berliarishabh/Mobile-Computing-and-IoT-Security----Final-Project-Repo/Photos and Screenshots/EnergyProfile_ScreenShots/BLE_OFF,SENSORS_ON.png

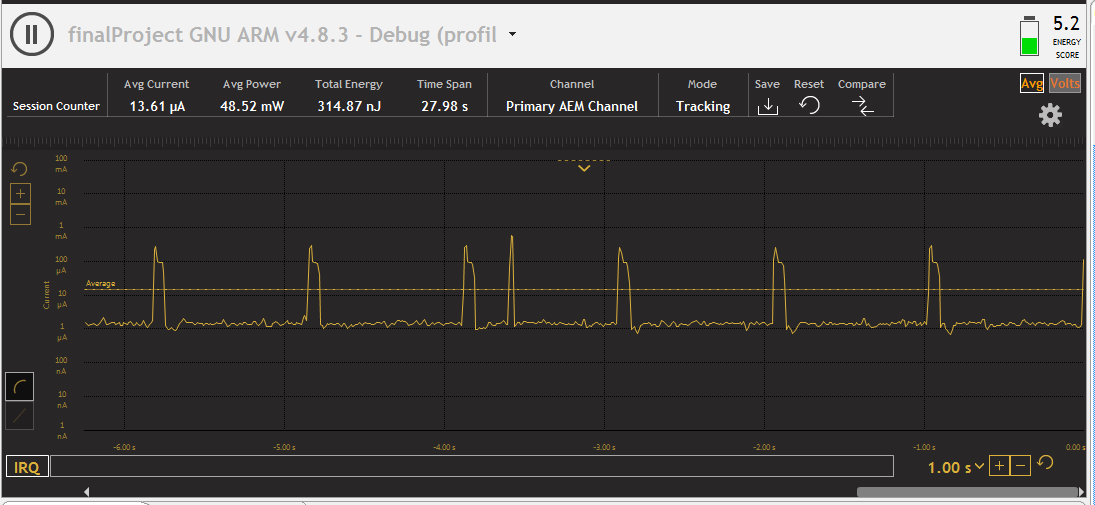
Photos and Screenshots/EnergyProfile_ScreenShots/BLE_OFF,SENSORS_ON.png
