berliarishabh/Mobile-Computing-and-IoT-Security----Final-Project-Repo/Photos and Screenshots/EnergyProfile_ScreenShots/Cap.png

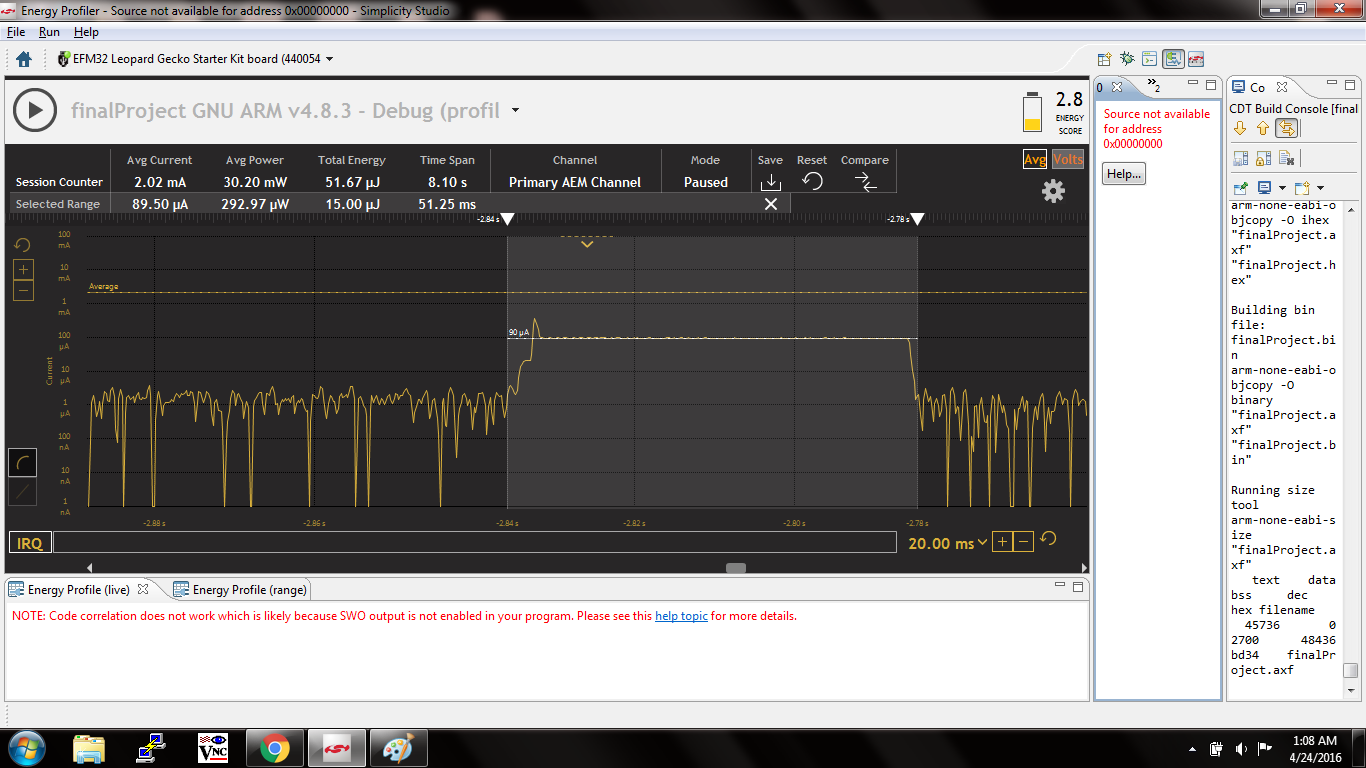
Photos and Screenshots/EnergyProfile_ScreenShots/Cap.png
