berliarishabh/Mobile-Computing-and-IoT-Security----Final-Project-Repo/Photos and Screenshots/EnergyProfile_ScreenShots/LC,Light,Cap-ON.png

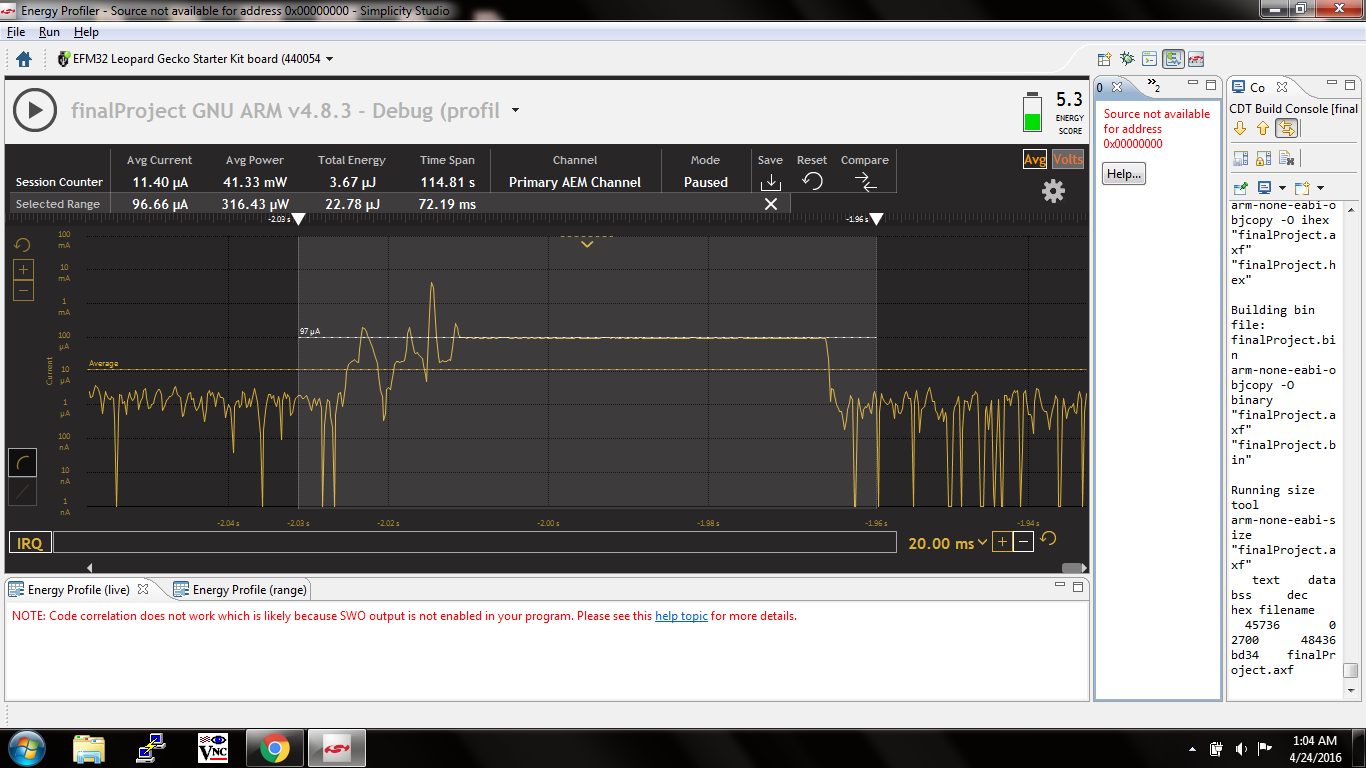
Photos and Screenshots/EnergyProfile_ScreenShots/LC,Light,Cap-ON.png
