berliarishabh/Mobile-Computing-and-IoT-Security----Final-Project-Repo/Photos and Screenshots/Project Photos/AccCube.JPG

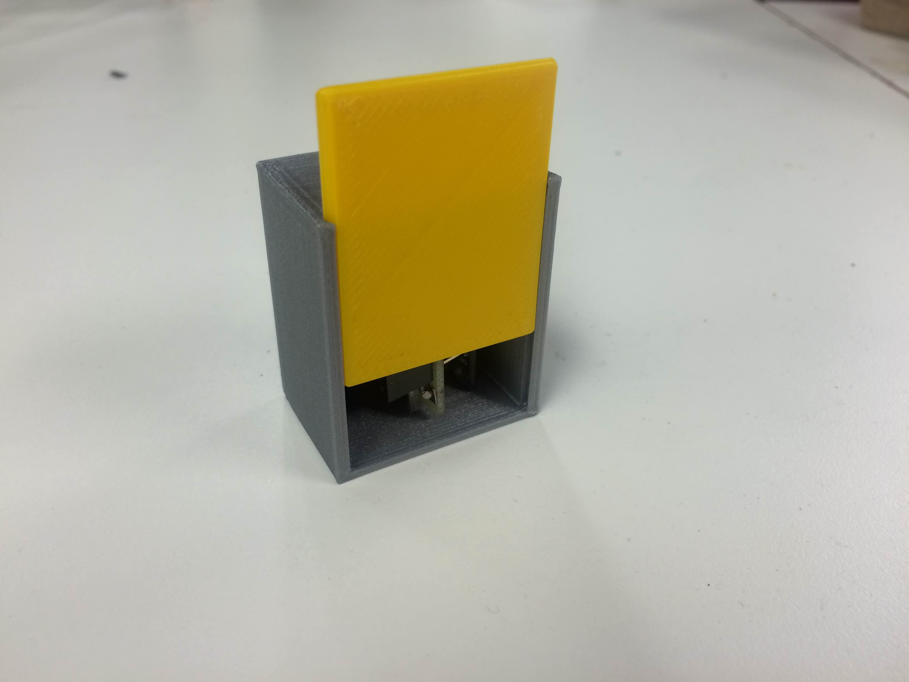
Photos and Screenshots/Project Photos/AccCube.JPG
