berliarishabh/Mobile-Computing-and-IoT-Security----Final-Project-Repo/Photos and Screenshots/Project Photos/IntelEdision.JPG

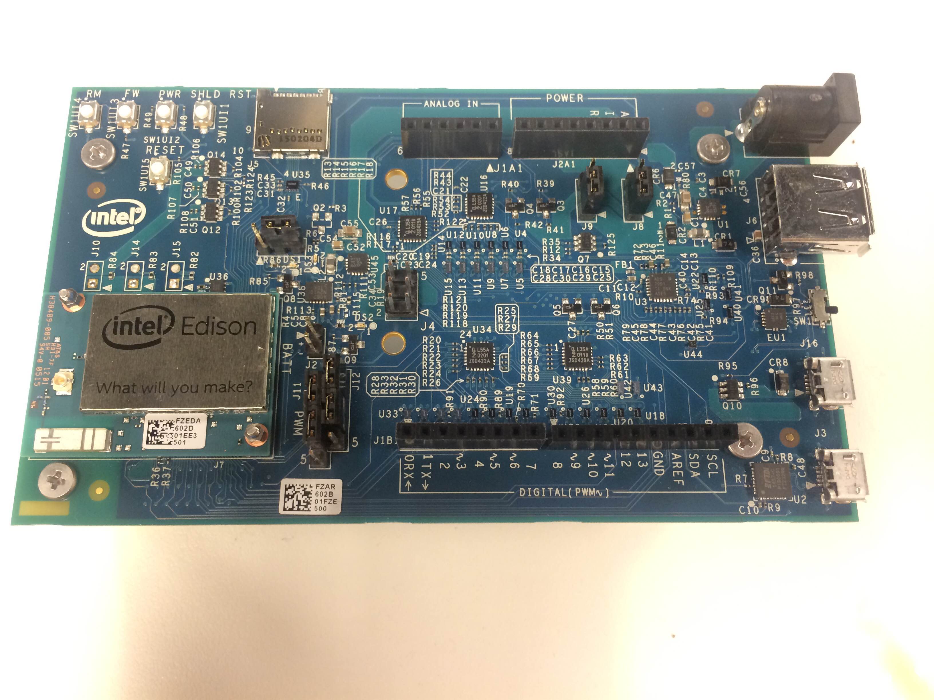
Photos and Screenshots/Project Photos/IntelEdision.JPG
