berliarishabh/Mobile-Computing-and-IoT-Security----Final-Project-Repo/Photos and Screenshots/Project Photos/LeopardGeckeCase_SIDE1.JPG

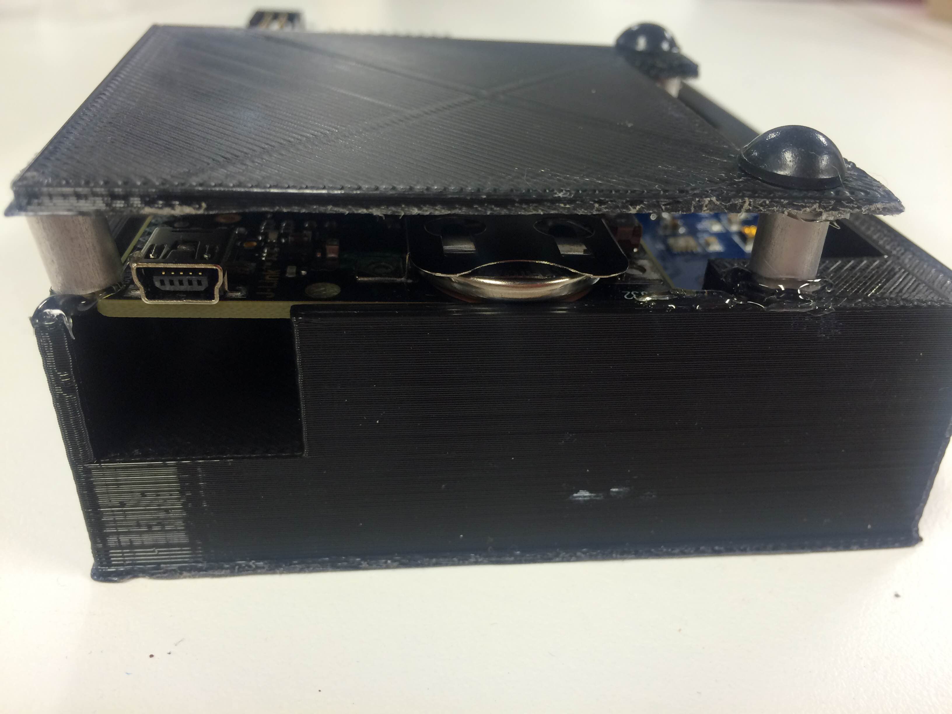
Photos and Screenshots/Project Photos/LeopardGeckeCase_SIDE1.JPG
