berliarishabh/Mobile-Computing-and-IoT-Security----Final-Project-Repo/Photos and Screenshots/Project Photos/LeopardGeckoinCase_TOP.JPG

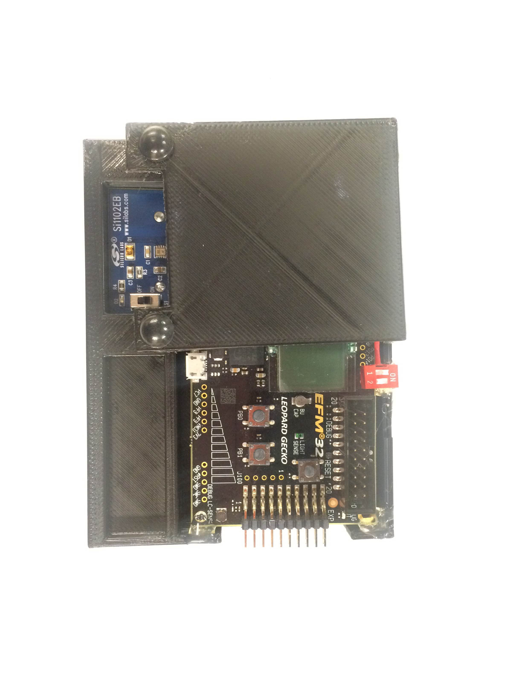
Photos and Screenshots/Project Photos/LeopardGeckoinCase_TOP.JPG
