berliarishabh/Mobile-Computing-and-IoT-Security----Final-Project-Repo/Photos and Screenshots/Project Photos/TI_SensorTag.JPG

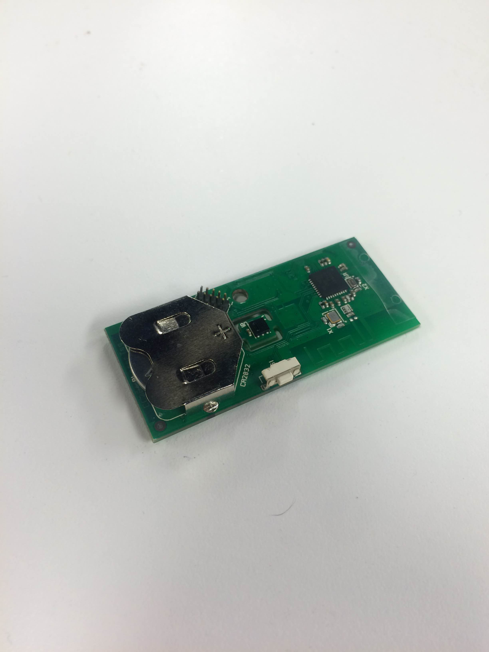
Photos and Screenshots/Project Photos/TI_SensorTag.JPG
