berliarishabh/Mobile-Computing-and-IoT-Security----Final-Project-Repo/Photos and Screenshots/ThingSpeak/Intel Edision Channel.png

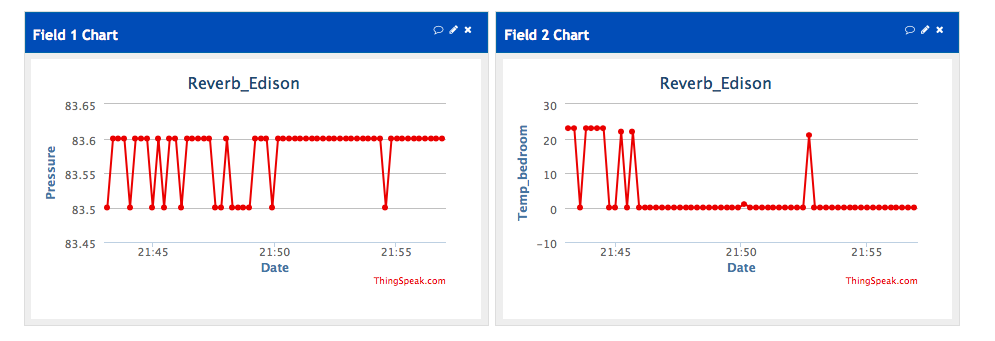
Photos and Screenshots/ThingSpeak/Intel Edision Channel.png
