berliarishabh/Mobile-Computing-and-IoT-Security----Final-Project-Repo/Photos and Screenshots/ThingSpeak/Photon Channel.png

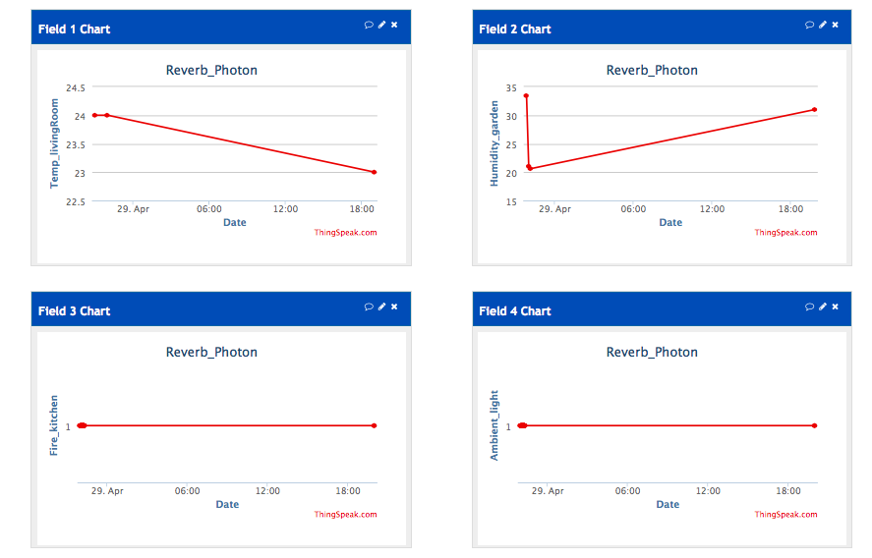
Photos and Screenshots/ThingSpeak/Photon Channel.png
