berliarishabh/Mobile-Computing-and-IoT-Security----Final-Project-Repo/Photos and Screenshots/ThingSpeak/Raspberry Pi (Leopard Gecko) Channel.png

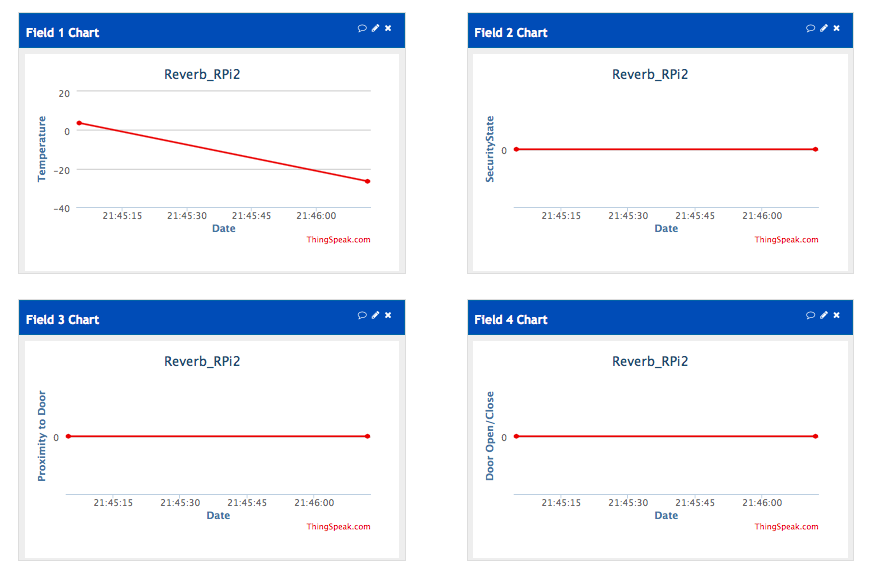
Photos and Screenshots/ThingSpeak/Raspberry Pi (Leopard Gecko) Channel.png
