berliarishabh/Mobile-Computing-and-IoT-Security----Final-Project-Repo/Photos and Screenshots/Twilio_Screenshot/Twilio.png

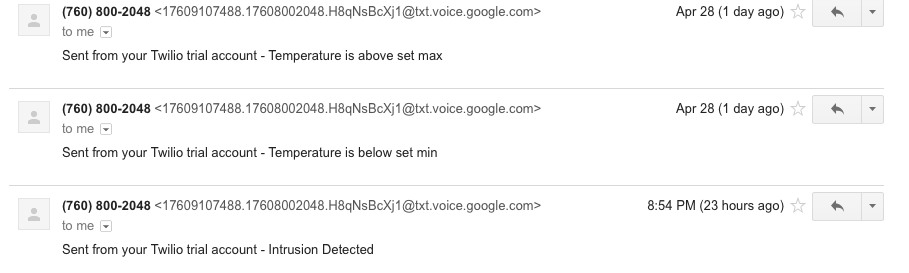
Photos and Screenshots/Twilio_Screenshot/Twilio.png
