berliarishabh/Mobile-Computing-and-IoT-Security----Final-Project-Repo/Photos and Screenshots/Twitter_Screenshot/Twitter.png

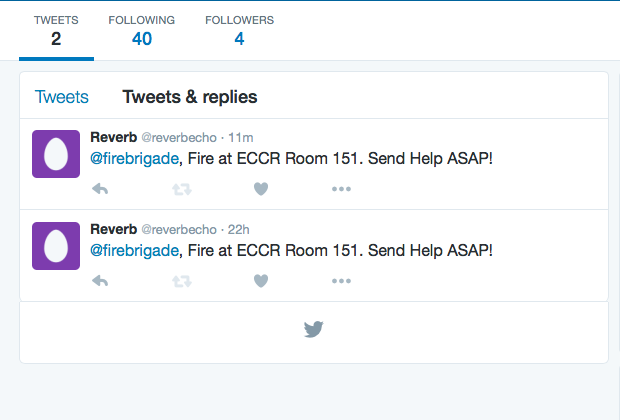
Photos and Screenshots/Twitter_Screenshot/Twitter.png
